tinyvision-ai-inc/UPduino-v3.0/assets/TVAI-FINAL-01-tight.png

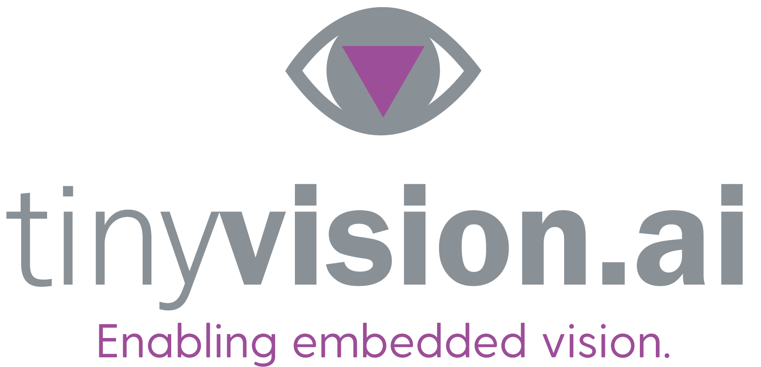
assets/TVAI-FINAL-01-tight.png
