tinyvision-ai-inc/UPduino-v3.0/assets/UPduino_v3.0_back.jpg

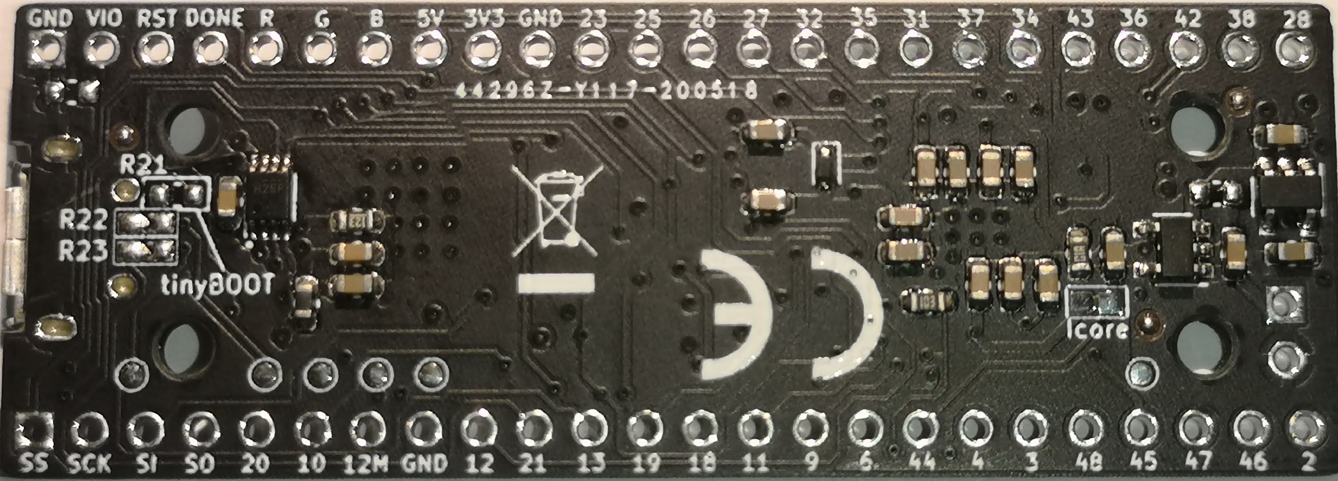
assets/UPduino_v3.0_back.jpg
