tinyvision-ai-inc/UPduino-v3.0/Board/KiCAD/Extended/UPduino.sch

## KiCad design Board/KiCAD/Extended/UPduino.sch (2019-12-03)

Schematic: UPduino.sch

Parts:
C1, C11, C19, C20, C21, C23, C24, C27, C28, C29: 4.7u; C_0603_1608Metric
C2, C3, C4, C5, C6, C7, C8, C9, C10, C12, C13, C14, C15, C16, C17, C18, C25, C31, C32: 0.1u; C_0603_1608Metric
C26: 10n; C_0603_1608Metric
C33, C34: DNI; C_0603_1608Metric
D1: HSMG-C120; LED_0603_1608Metric
D2: 1N4148W; D_SOD-123
D3: MHPA1515RGBDT-S; LED_Cree-PLCC4_2x2mm_CW
FB1, FB2, FB3: BLM18HE152SN1D; L_0603_1608Metric
FID1, FID2, FID3, FID4, FID5, FID6: Fiducial; Fiducial_0.5mm_Mask1mm
H1, H2, H3, H4: MountingHole; MountingHole_3.2mm_M3
J1: 47589-0001; USB_Micro-B_Molex-105017-0001
J2: Right; PinHeader_1x24_P2.54mm_Vertical
J3: Left; PinHeader_1x24_P2.54mm_Vertical
J4: 5V Power; PinHeader_1x02_P2.54mm_Vertical
R1, R3, R7: 2.2K; R_0603_1608Metric
R2, R4, R5, R8, R9, R14, R15, R17, R18: 10K; R_0603_1608Metric
R6: 100; R_0603_1608Metric
R10, R21: DNI; R_0603_1608Metric
R11, R12, R13: 27; R_0603_1608Metric
R16, R19, R20, R22, R23, R24, R25, R26, R27, R31, R35, R36: JUMPER; R_0603_1608Metric
R34: 0; R_0603_1608Metric
RN1: YC124-JR-071KL; R_Array_Concave_4x0402
S1: TC7MPB9327FK(EL); WSON-14-1EP_4.0x4.0mm_P0.5mm_EP2.6x2.6mm; Manufacturer_Part_Number TC7MPB9327FK(EL)
TP1, TP2, TP3, TP4, TP5, TP6, TP7, TP8, TP9, TP10, TP11, TP12: TestPoint; TestPoint_Pad_D1.0mm
U1: 93LC56BT-I/OT; SOT-23-6
U2: ICE40UP5K-SG48ITR; QFN-48-1EP_7x7mm_P0.5mm_EP5.6x5.6mm
U3: FT232H; QFN-48-1EP_7x7mm_P0.5mm_EP5.45x5.45mm
U4: SG-210STF 12.0000ML3; Oscillator_SMD_Abracon_ASDMB-4Pin_2.5x2.0mm
U5: W25Q32JVSSIM; SOIC-8_5.23x5.23mm_P1.27mm
U6: AP2127K-3.3; SOT-23-5
U7: AP2127K-1.2; SOT-23-5

Notes on the sheet:
tinyFPGA Bootloader
FTDI programmer
FPGA Power
FPGA Banks
12MHz Oscillator
qSPI/DTR Flash
LED
Regulators (300mA max)
Board Connections
FPGA CRAM/Flash programming
This mode requires the flash to be programmed with the tinyFPGA bootloader. To enable: - Program Flash with bootloader - Short C26 - Open R35, 36 - Install R22, R23 (68 Ohms) - Install R21 (1.5K) - Enjoy!
Programming modes: Flash: programmed when reset is held low CRAM: programmed when reset is held high
Bank 0
Bank 1
Bank 2
Install jumper to enable 12MHz clock to the FPGA
TODO: - Finalize header pinout - Check on programming scheme
Old pinout
New addition
Bank 1 is 3.3V IO!
Install 0 Ohms for qSPI
Core current measurement
Layout note: These pins may be moved anywhere within Bank 1 except the SPI pins or pin 20
3.3V
1.2V
Reqd for backward compatibility with v2
Layout note: Place these testpoints on the bottom of the board on a 2.54mm grid.
